fl4p/Fugu2/doc/Reverse Recovery Qrr.md

https://link.springer.com/chapter/10.1007/978-3-642-15739-4_12

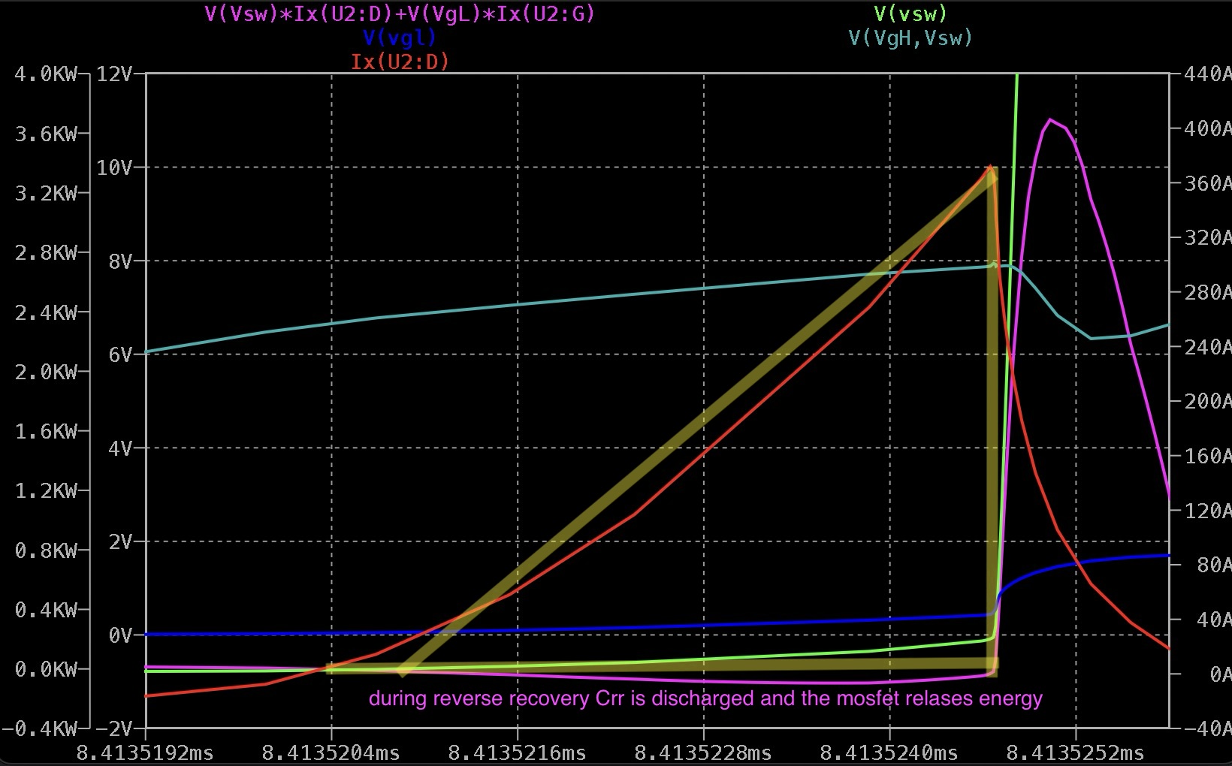
[picture p52: doc/img/mosfet-qrr-plot.jpg]

mosfet qrr.webp
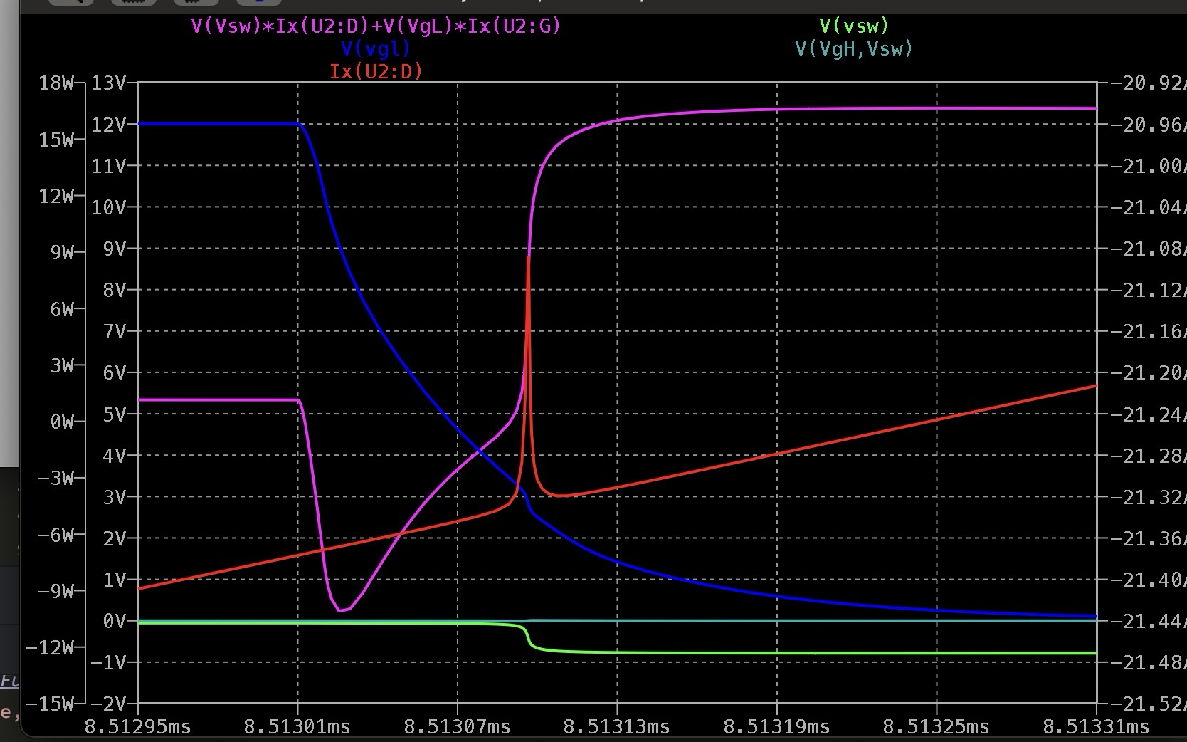
[picture p53: doc/img/mosfet-rr-charge-plot.jpg]
