fl4p/Fugu2/HW Stories/fboost.md

- operates in boost mode
- backflow-switch shorted
- LS: IPP022n12n6 (rg=4.7), external schottky diode
- hs: ip040 (2p but only 1 used) (rg=7.5, rg_dis=7.5/2)
