fl4p/Fugu2/HW Stories/fetlib.md

# testboard1
- HS: 2p IPP055
- LS: IPP024 (no external diode)

next:
- LS: FDP027
