fl4p/Fugu2/doc/Fuse.md

# SMD

0685H9300-01 (30A, 1.1mΩ, 1.59W)

# Micro Blade
0327030.YX2S (30A, 2.1mΩ)

# Mini Blade
0297030.U 1.85m

# Blade
0287035.PXCN 35A 1.61m

# SMD

60V, 20A: JAK 6002203 NA52

# Catridge
60V, 40A: AXT 40A 60V (PF)
