fl4p/Fugu2/doc/Enclosures.md

F-Type connectors (SAT)
