fl4p/Fugu2/doc/PCBway.md

## Assembly

* [Can we buy components from specific supplier or provide link for purchasing?](https://www.pcbway.com/helpcenter/pcb_assembly_ordering/Can_we_buy_components_from_specific_supplier_or_provide_link_for_purchasing_.html)
* [“BOM template”](http://www.pcbway.com/img/images/pcbway/Sample_BOM_PCBWay.xlsx)
* [Can I list capacitors or resistors in BOM without exact part numbers?](https://www.pcbway.com/helpcenter/pcb_assembly_ordering/Can_I_list_capacitors_or_resistors_in_BOM_without_exact_part_numbers_.html)

```
Resistor:
10K 0805 1%
10R 0603 5%

Capacitor:
0.1μF 0805 25V x7r
10nF 0603 25V C0G   

```
