fl4p/Fugu2/doc/Diodes.md

| | DC block | Vrms | Iavg | Ipeak | Vfwd@1A | C pF@4V,1MHz |
|---|---|---|---|---|---|---|
| 1N5819WS | 40 | 28 | 1 | 25 | 0.6, 0.9@3A | 110 |
| MSS1P4 | 40 | | 1 | 25 | 0.41, | 50 |
| SS310 | 100 | 70 | 3 | 80 | 0.85@3A | 300 |
| 1N4148W-7-F | | | | | | |
| | | | | | | |
| | | | | | | |
