fl4p/Fugu2/doc/img/mosfet-hs-turn-off.webp

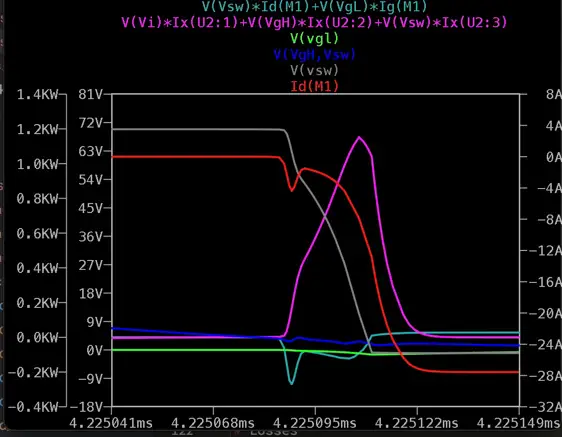
doc/img/mosfet-hs-turn-off.webp
