fl4p/Fugu2/doc/img/mosfet-self-turn-on-waveform-power.webp

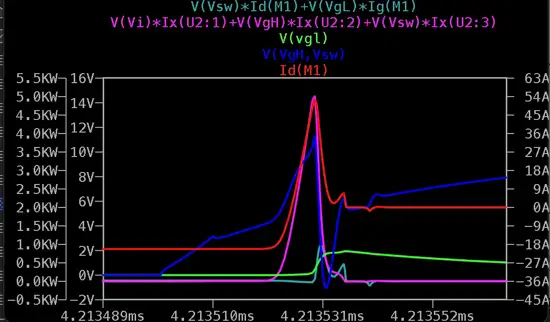
doc/img/mosfet-self-turn-on-waveform-power.webp
