fl4p/Fugu2/doc/img/UCC21330x-layout.webp

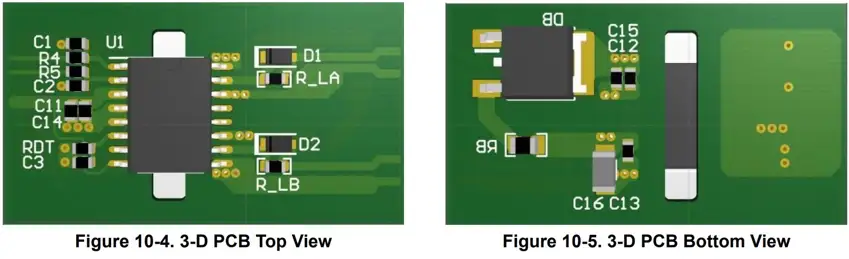
doc/img/UCC21330x-layout.webp
