fl4p/Fugu2/img/fmetal-water-console.webp

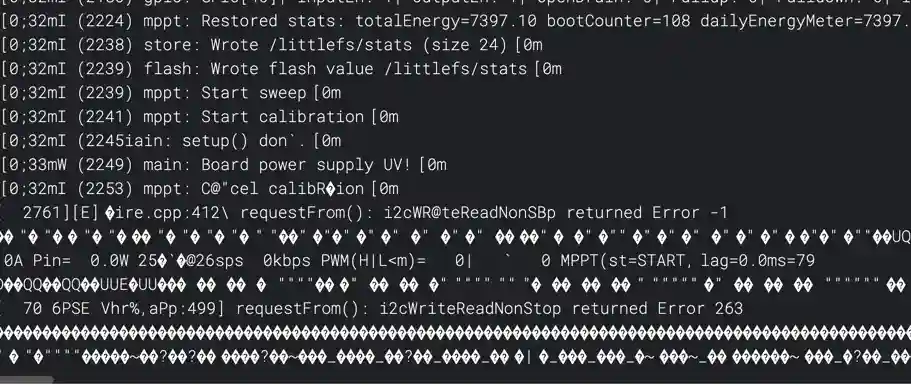
img/fmetal-water-console.webp
