fl4p/Fugu2/img/TR000132-fugu2-T130.webp

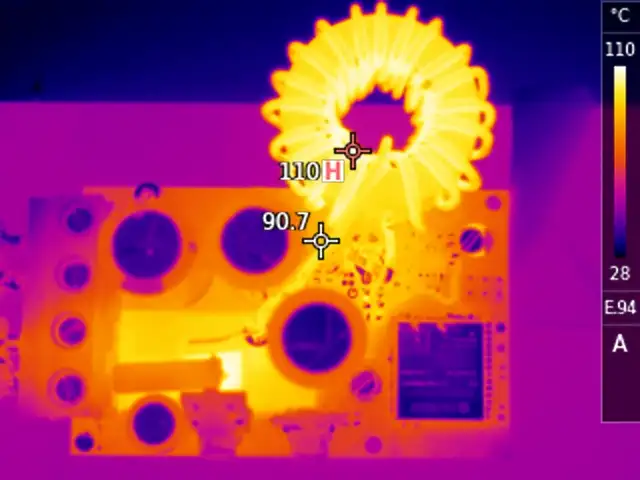
img/TR000132-fugu2-T130.webp
