fl4p/Fugu2/img/TR000135-fugu2.webp

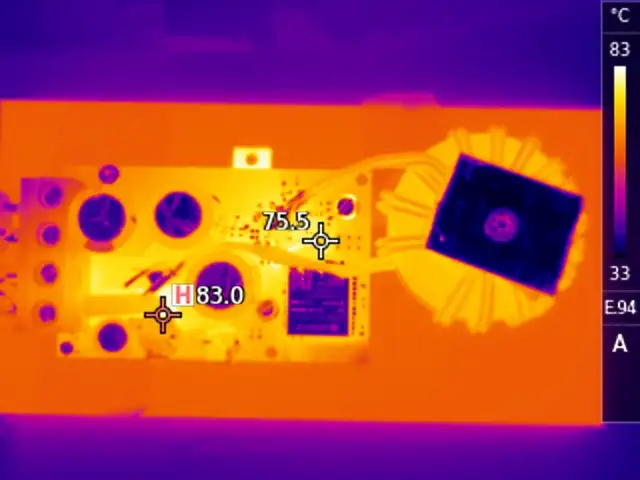
img/TR000135-fugu2.webp
