fl4p/Fugu2/img/TR000137-fugu2-fan.webp

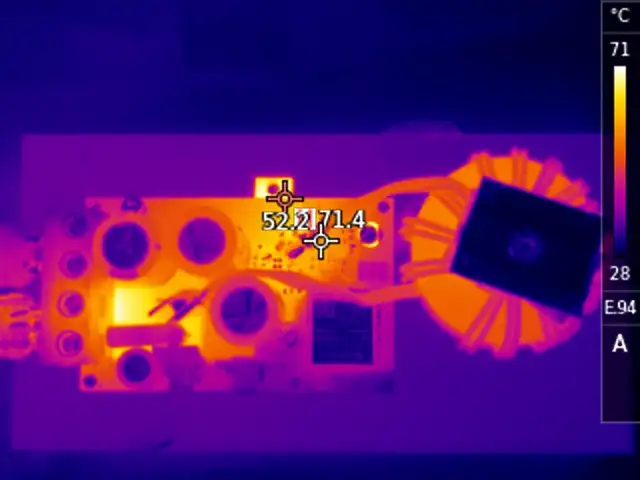
img/TR000137-fugu2-fan.webp
