fl4p/Fugu2/spice/extract/c18_geometry.png

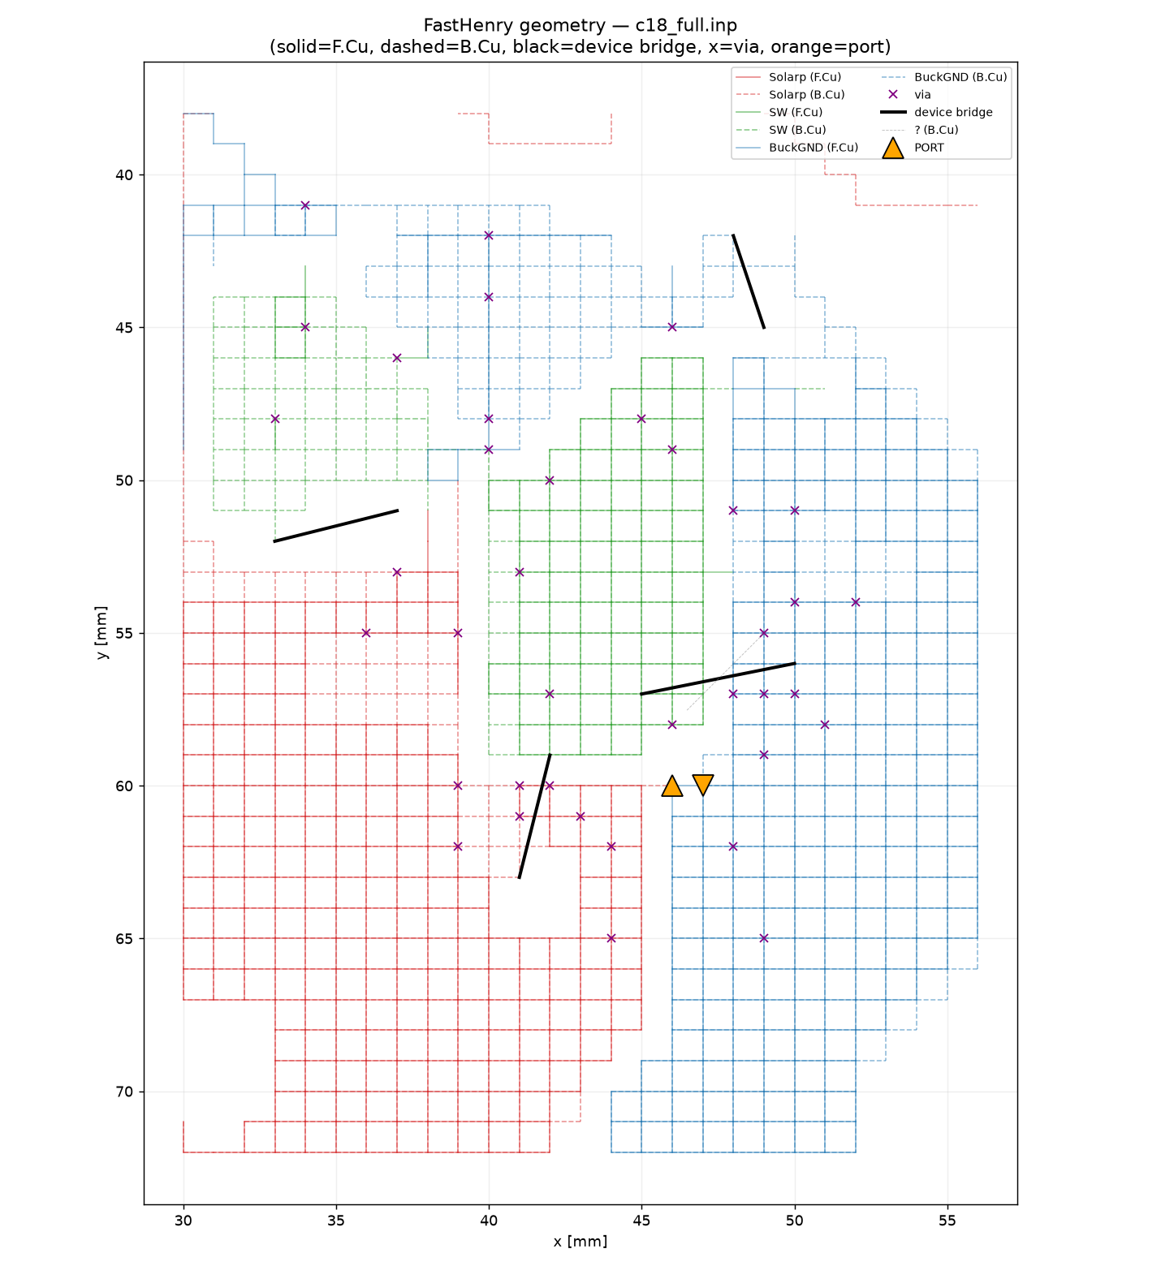
spice/extract/c18_geometry.png
