fl4p/Fugu2/spice/fugu2_loss_budget.png

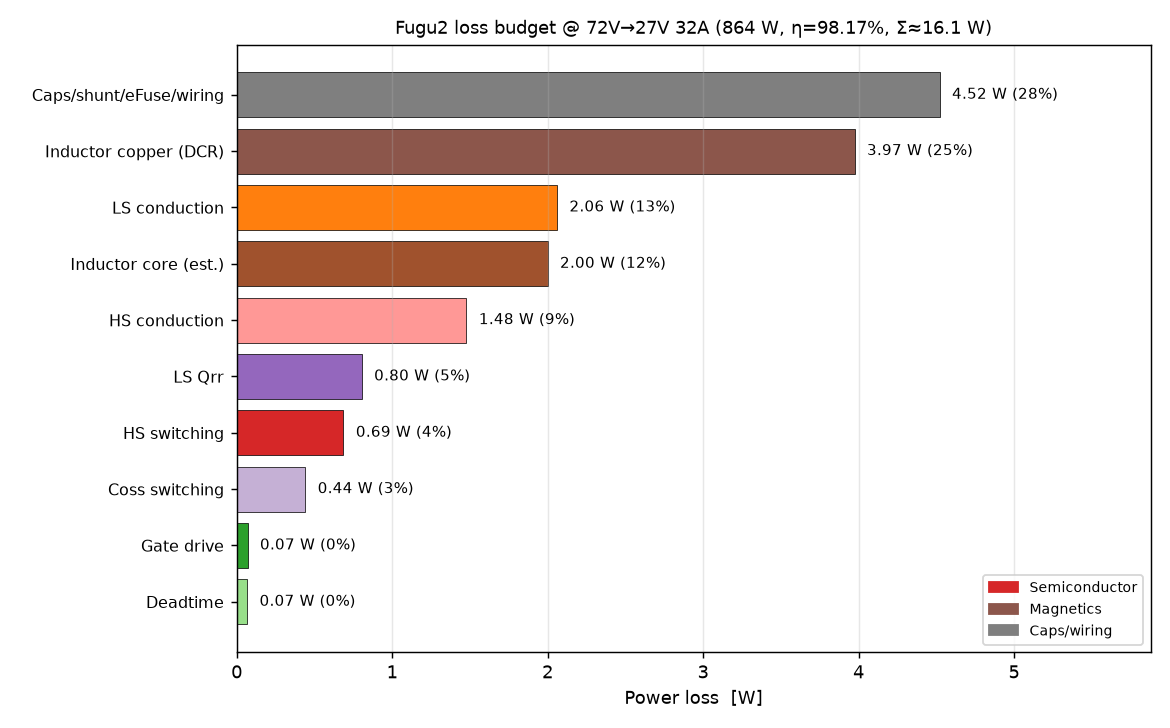
spice/fugu2_loss_budget.png
