fl4p/Fugu2/spice/spice-fit/st15100s/reference/ST15100_fig1_curves.png

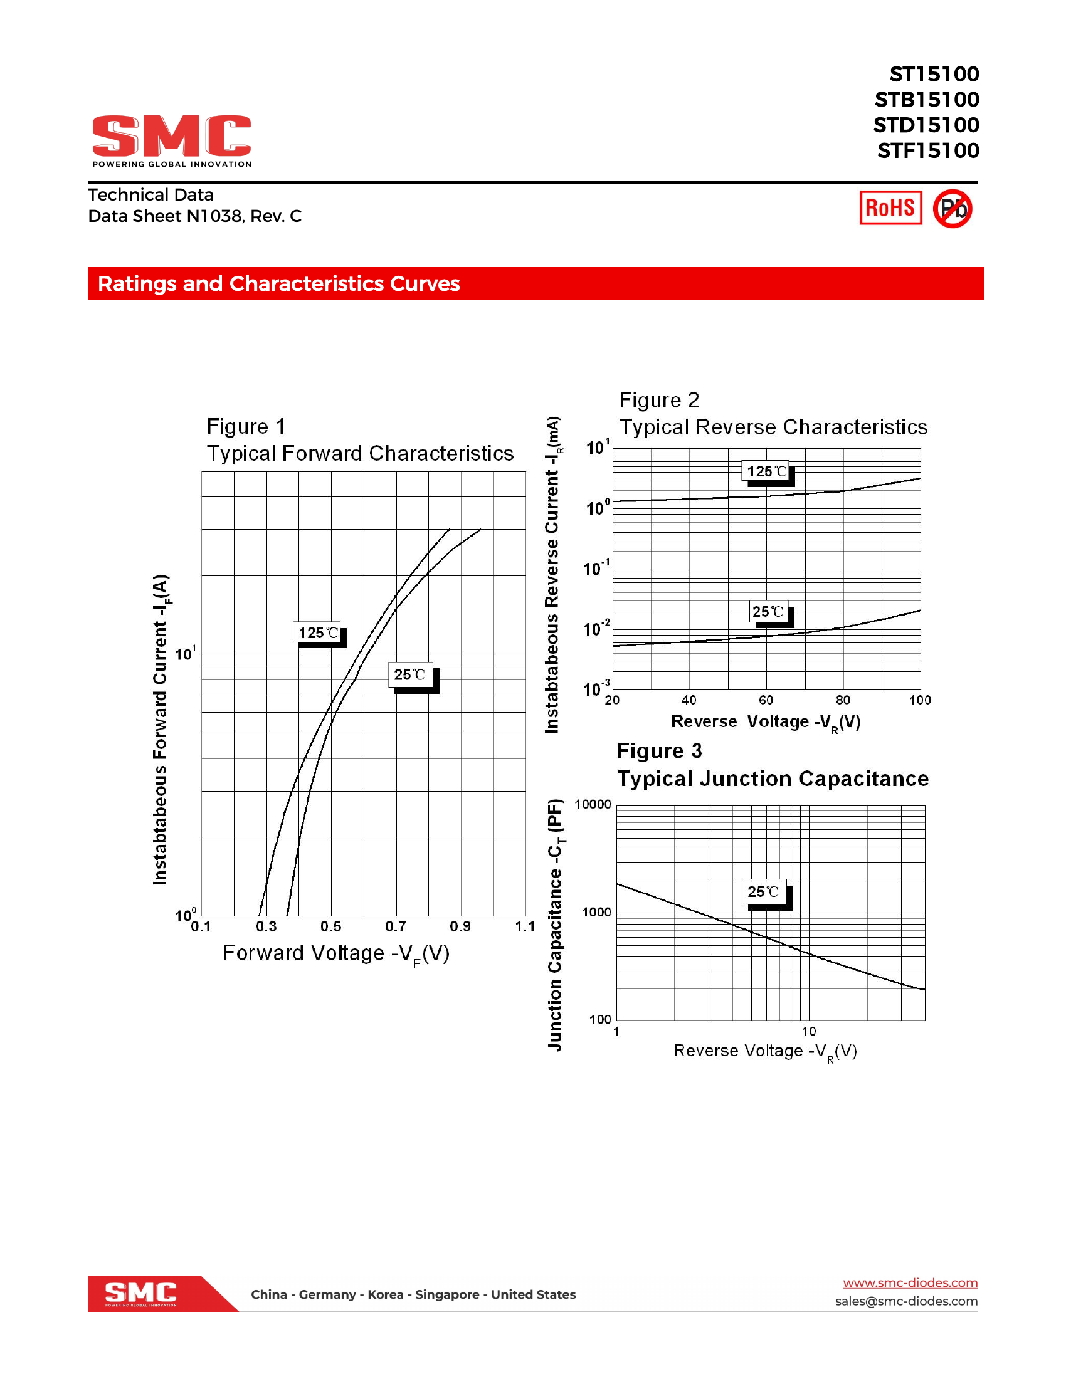
spice/spice-fit/st15100s/reference/ST15100_fig1_curves.png
