fl4p/Fugu2/spice/spice-fit/st15100s/reference/ST15100S_fig1_forward_400dpi.png

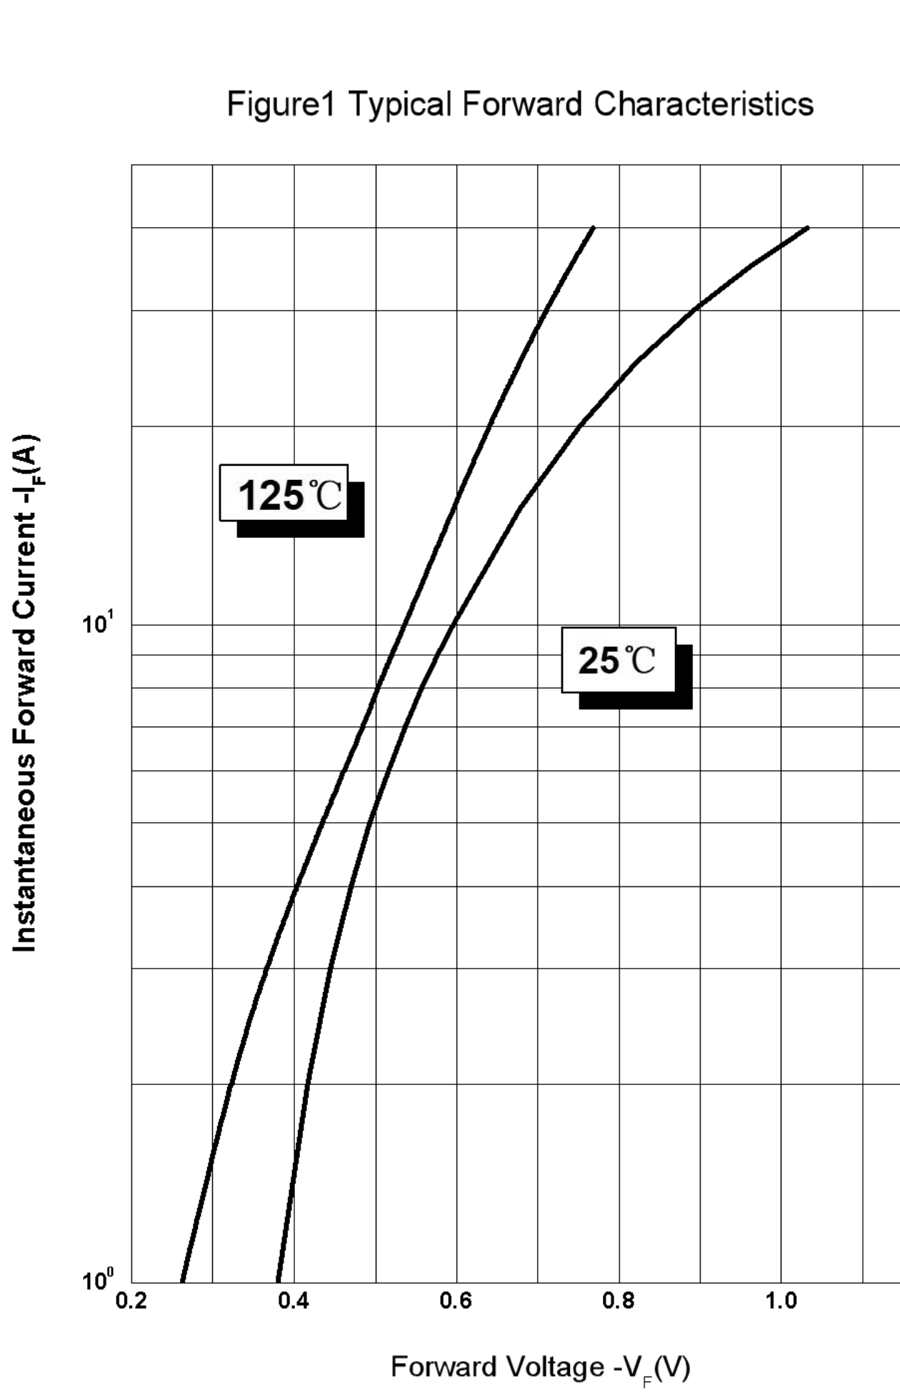
spice/spice-fit/st15100s/reference/ST15100S_fig1_forward_400dpi.png
