fl4p/Fugu2/spice/spice-fit/svt15100ub/reference/SVT15100UB_fig2_cap.png

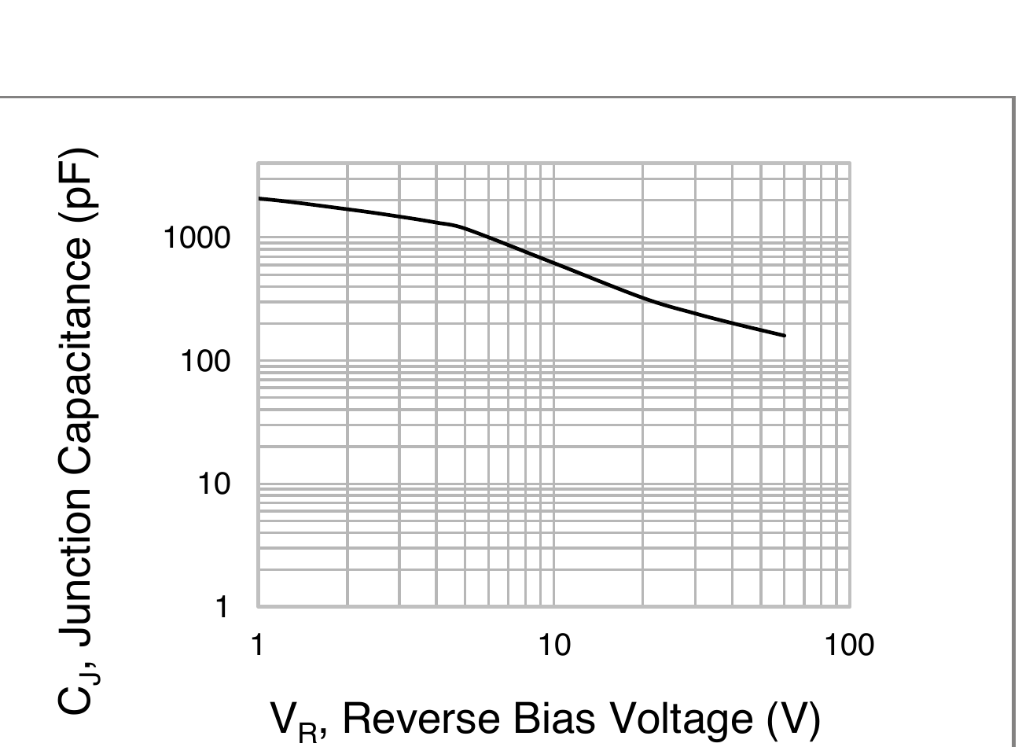
spice/spice-fit/svt15100ub/reference/SVT15100UB_fig2_cap.png
