fl4p/Fugu2/spice/spice-fit/svt15100ub/reference/SVT15100UB_fig4_forward.png

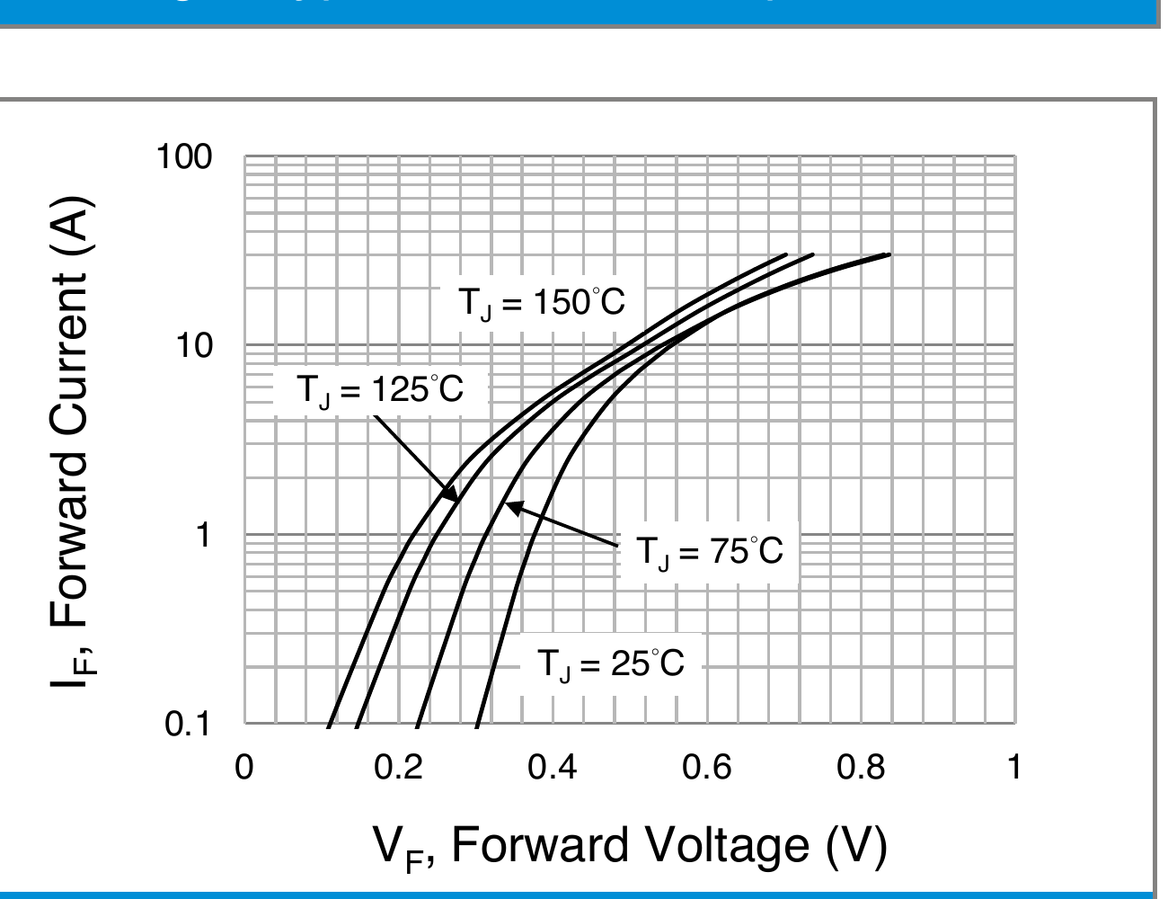
spice/spice-fit/svt15100ub/reference/SVT15100UB_fig4_forward.png
