fl4p/Fugu2/spice/buck_parasitcs_extracted.asc

C1: cap; 470�
C2: polcap; 470�; Rser=36m Lser=11n mfg="W�rth Elektronik" pn="860040880011 WCAP-ATUL 16x35,5" type="Al electrolytic"
C3: polcap; 470�; Rser=36m Lser=11n mfg="W�rth Elektronik" pn="860040880011 WCAP-ATUL 16x35,5" type="Al electrolytic"
D2: diode; 1N4148
D3: schottky; RB228NS150
D4: diode; 1N4148
L1: ind; 60�; Rser=5m
L2: ind; 40n
L3: ind; 40n
L4: ind; 2n; Rser=10u Rpar=1 Cpar=100p
L5: ind; 2n; Rser=10u Rpar=1 Cpar=100p
L6: ind; 10n; Rser=10u Rpar=1 Cpar=100p
L8: ind; 1�; Rser=10m
R1: Res; 10
R2: Res; 15
R3: res; 1.3; IC=2
R4: Res; 3
R5: Res; 7
U1: TK3R2A08QM
U2: TK3R2A08QM
V1: voltage; PULSE(0 12 13500n 10n 10n 11500n 25000n)
V2: voltage; PULSE(0 12 500n 10n 10n 12500n 25000n)
V3: voltage; 70
Named nets: 0, Vo, Vsw, Vi, VgL, VgH, VdrvL, VdrvHO
.tran 9000u
FET models: manufacturer-only. HS/LS = Toshiba TK6R8A08QM_G0_00 (mfr, standard-primitive,
converges cleanly). 120V LS option = Infineon IPP022N12NM6_L0 (mfr die-only + external leads).
Do NOT use community libs or Infineon _L1 subckts (numerically fragile). See PARASITIC_MODELING.md.
FastHenry-extracted Cin hot-loop bypass (vendor cap models + per-cap copper branch L).
Shared switch-loop copper = L5(2n)+L4(2n)=4.0nH; per-cap branch L in cin_hotloop.lib.
Electrolytics C2/C3 remain as the slow bulk path (now carry little HF current).
.inc extract/capmodels/vendor/MMASH21GBC7105_TCA01_LT.cir
.inc extract/capmodels/vendor/MCASH168SC7224_TCA01_LT.cir
.inc extract/capmodels/vendor/c21c22_10u_2220_GRM32EC72A106KE05.mod
.inc extract/capmodels/cin_hotloop.lib
.inc extract/capmodels/fets/TK6R8A08QM_G0_00_PSpice_rev1.lib
XCIN Vi 0 Cin_hotloop
FETs: U1(HS, x2 Q1||Q3) and U2(LS) = Toshiba TK6R8A08QM_G0_00 (mfr). Add external TO-220
leads Ld=2.5n Ls=2n Lg=4n per device (the _G0 model has no built-in leads). Loop L=13nH (4 copper+9 leads).
AUTHORITATIVE converged 32A/80V stress: dpt_toshiba.cir -> SW peak 85.7V, overshoot 5.68V (Qrr included).
120V LS margin check: dpt_mixed.cir (Toshiba HS + IPP022N12NM6_L0 LS) -> SW peak ~99V.
