fl4p/Fugu2/spice/buck.asc

C1: cap; 470µ
C2: cap; 470µ
D2: diode; 1N4148
D3: schottky; RB228NS150
D4: diode; 1N4148
L1: ind; 60µ; Rser=5m
L2: ind; 40n
L3: ind; 40n
L4: ind; 2n; Rser=10u Rpar=1 Cpar=100p
L5: ind; 1n; Rser=10u Rpar=1 Cpar=100p
L6: ind; 10n; Rser=10u Rpar=1 Cpar=100p
R1: Res; 10
R2: Res; 15
R3: res; 1.3
R4: Res; 3
R5: Res; 7
U1: TK3R2A08QM
U2: TK3R2A08QM
V1: voltage; PULSE(0 12 13500n 10n 10n 11500n 25000n)
V2: voltage; PULSE(0 12 500n 10n 10n 12500n 25000n)
V3: voltage; 70
Named nets: 0, Vo, Vsw, Vi, VgL, VgH, VdrvL, VdrvHO
.tran 9000u
.inc CSD19506KCS.lib
.inc STP110N8F6_V2.lib
.inc TK7R0E08QM_G0_00_PSpice_rev1.lib
