fl4p/Fugu2/spice/buck_sync_sw.asc

C1: cap; 470µ
C2: cap; 470µ
C3: cap; 10µ
D1: diode; 1N4148
D3: schottky; RB228NS150
L1: ind; 60µ; Rser=5m
M1: nmos; AONS66811
M2: nmos; IPB019N08N3
R1: Res; 6
R2: Res; 6
R3: res; 1.3
U1: IR2184
V1: voltage; PULSE(0 12 13500n 10n 10n 11500n 25000n)
V2: voltage; PULSE(0 12 500n 10n 10n 12500n 25000n)
V3: voltage; 70
V4: voltage; PULSE(0 3.3 12600n 10n 10n 12500n 25000n 6)
V5: voltage; 0
Named nets: 0, Vo, Vsw, Vi, VgL, VgH, VdrvL, VdrvHO
.tran 6000u
.inc ir2184.lib
.inc CSD19506KCS.lib
